suskaroobert/elektronicky.ziarivkovy.predradnik/media/20250525_101839.jpg

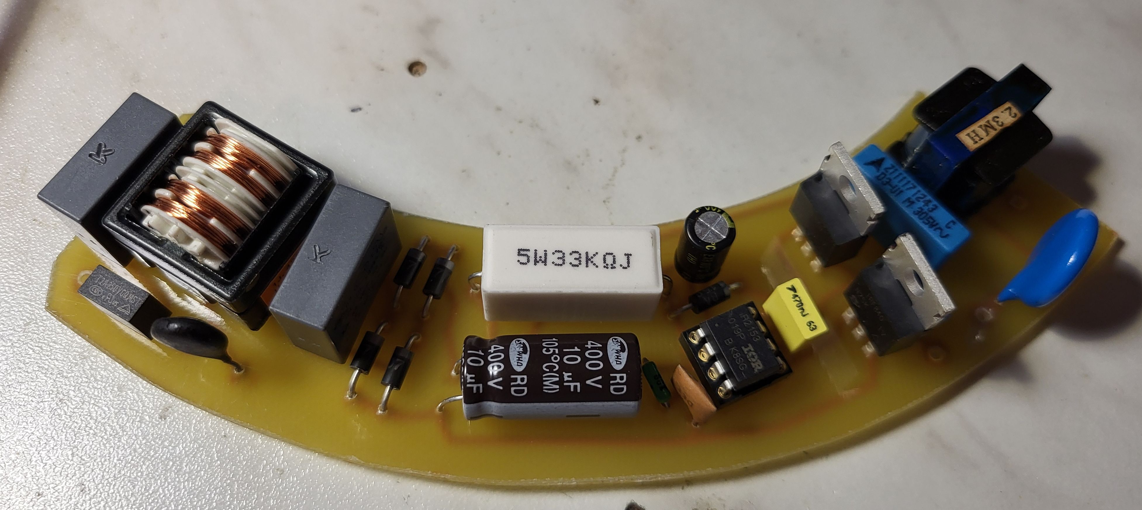
media/20250525_101839.jpg
