suskaroobert/elektronicky.ziarivkovy.predradnik/media/20250525_101849.jpg

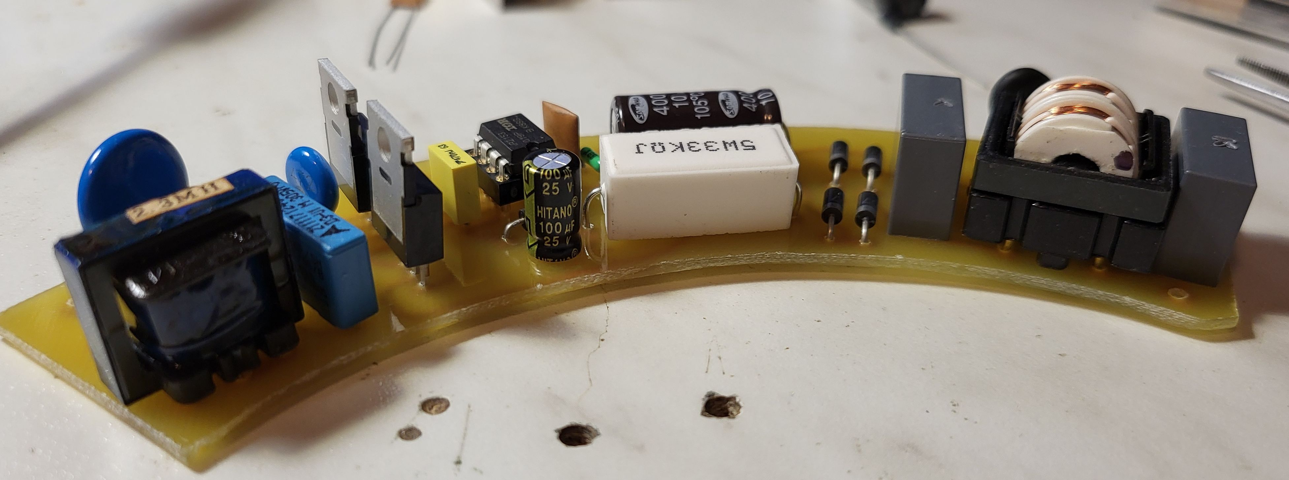
media/20250525_101849.jpg
