suskaroobert/elektronicky.ziarivkovy.predradnik/media/20250525_101857.jpg

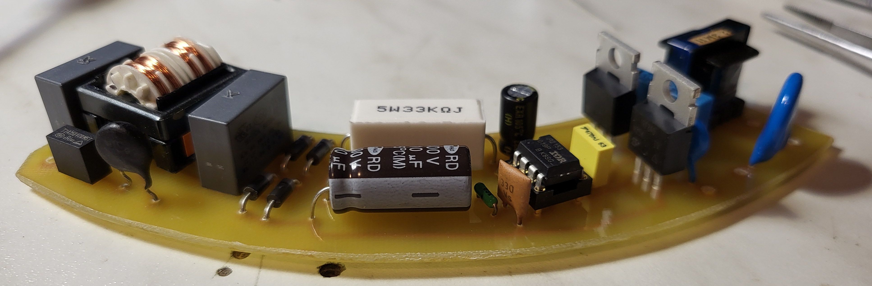
media/20250525_101857.jpg
