suskaroobert/elektronicky.ziarivkovy.predradnik/media/20250525_130345.jpg

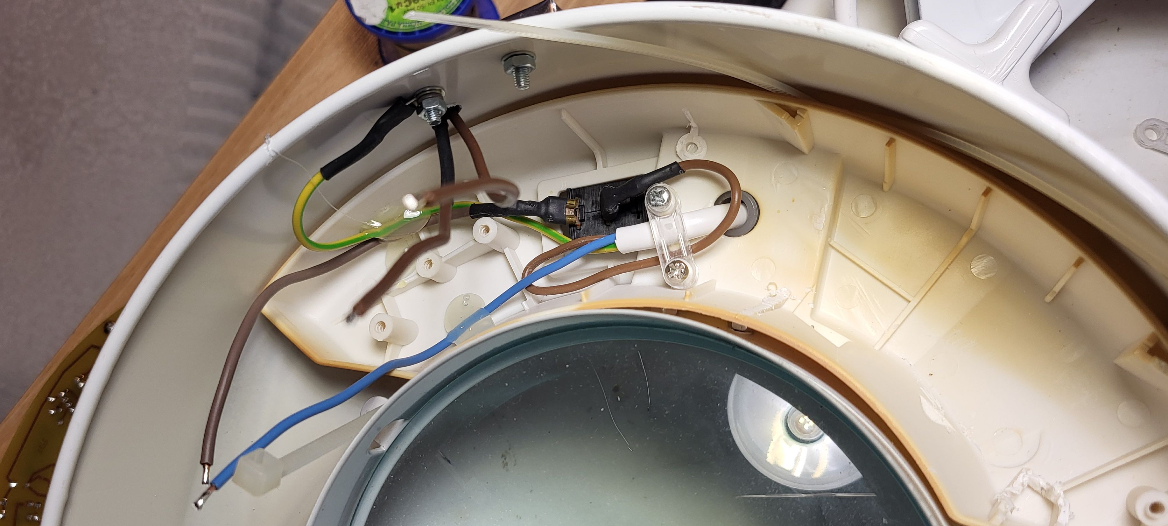
media/20250525_130345.jpg
