suskaroobert/elektronicky.ziarivkovy.predradnik/media/20250525_131243.jpg

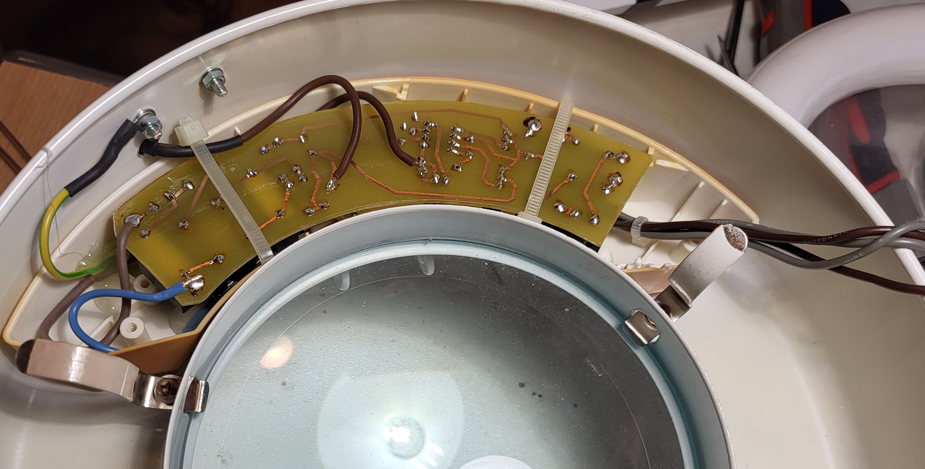
media/20250525_131243.jpg
