suskaroobert/elektronicky.ziarivkovy.predradnik/media/20250525_135439.jpg

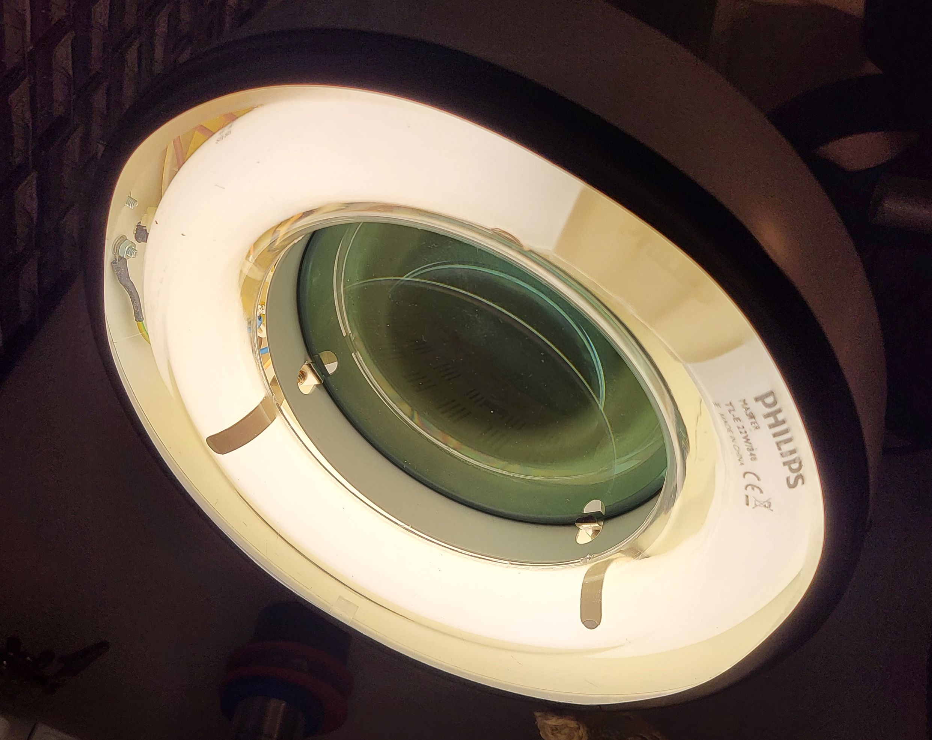
media/20250525_135439.jpg
