suskaroobert/elektronicky.ziarivkovy.predradnik/media/20250525_161053.jpg

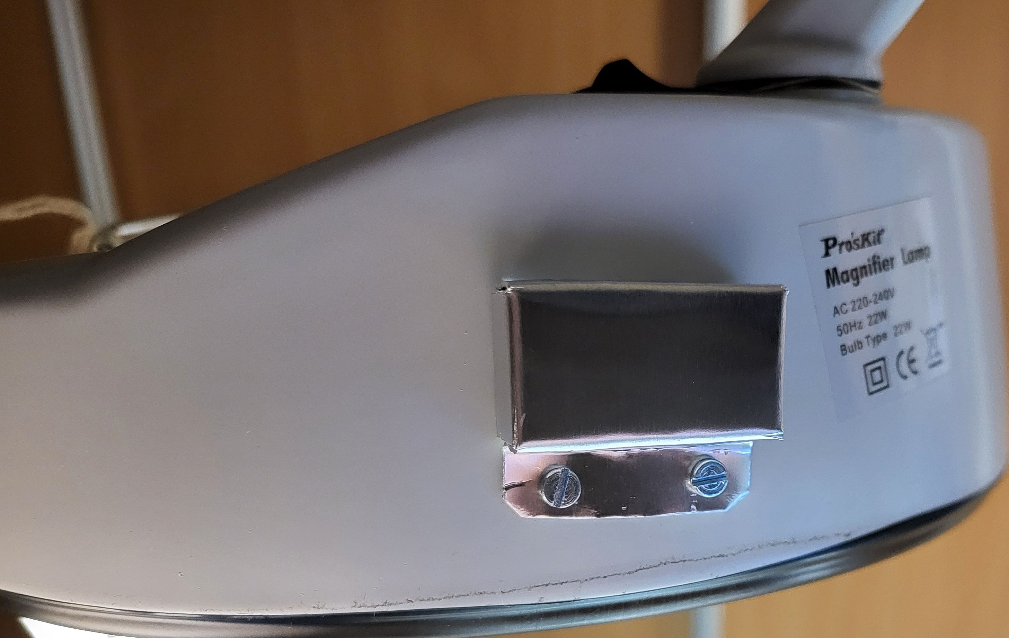
media/20250525_161053.jpg
